alvarini/BlindTech/3D_CAD/image019.jpg

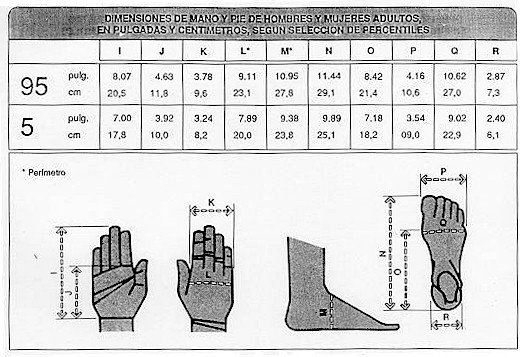
3D_CAD/image019.jpg
