alvarini/BlindTech/figuras/Area de barrido.PNG

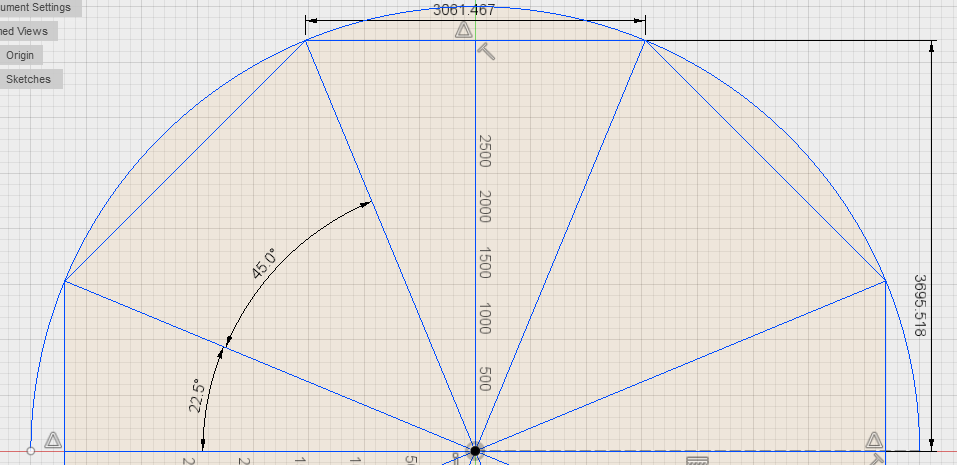
figuras/Area de barrido.PNG
