alvarini/BlindTech/figuras/qlearning.jpg

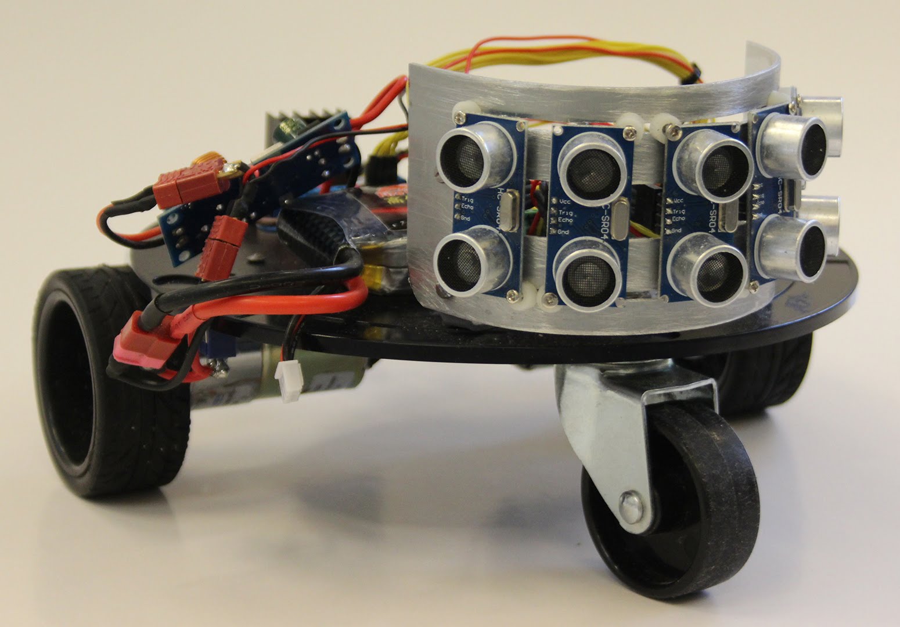
figuras/qlearning.jpg
