alvarini/BlindTech/img/profile.png

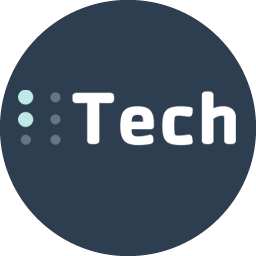
img/profile.png
